Aviral212011/INDIKEY/images/Screenshot 2026-07-25 134537.png

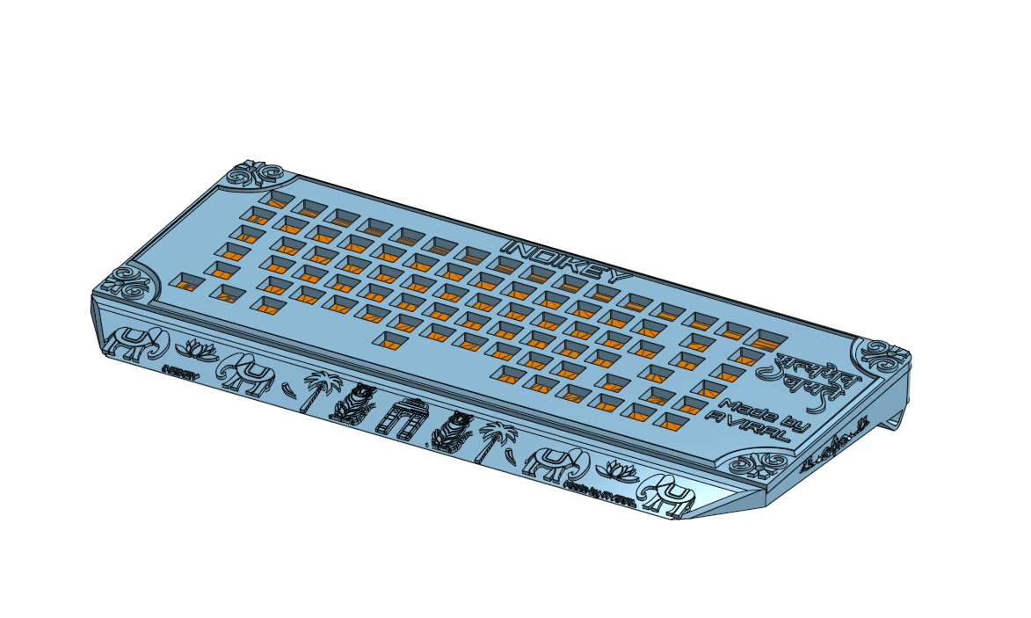
images/Screenshot 2026-07-25 134537.png
