Aviral212011/INDIKEY/images/Screenshot 2026-07-25 135355.png

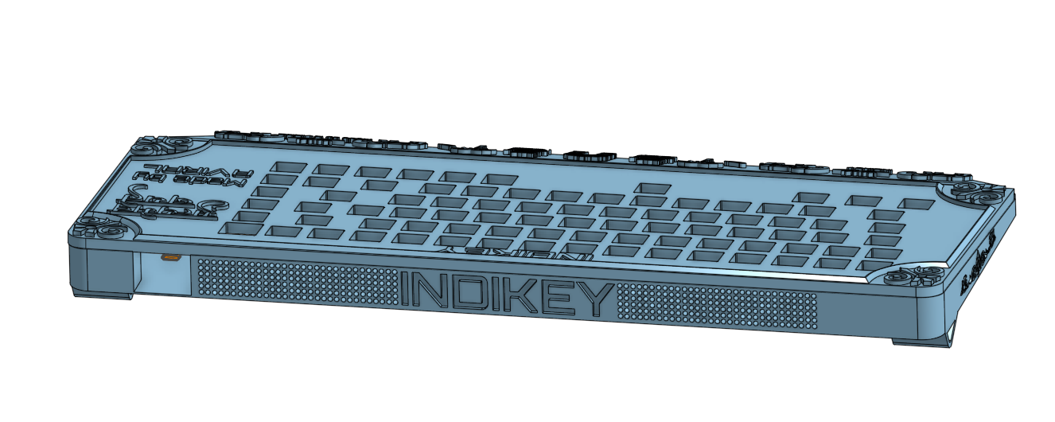
images/Screenshot 2026-07-25 135355.png
