Aviral212011/INDIKEY/images/Screenshot 2026-07-25 135700.png

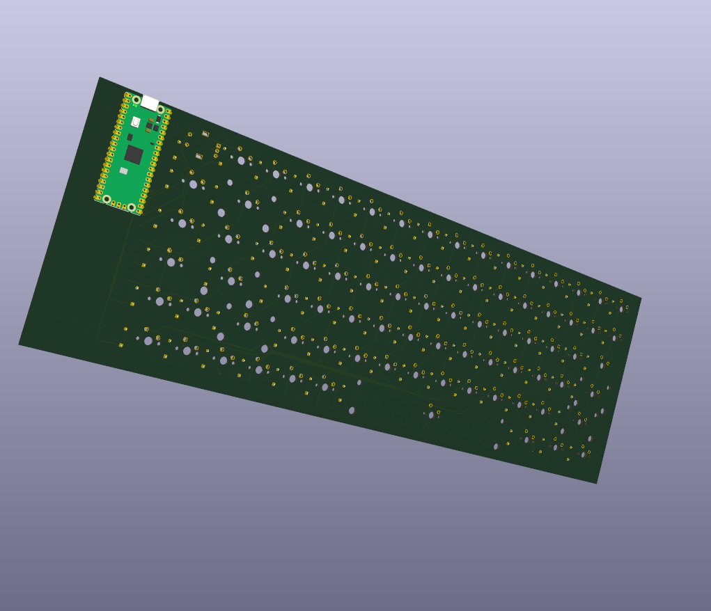
images/Screenshot 2026-07-25 135700.png
