Aviral212011/INDIKEY/images/Screenshot 2026-07-25 135743.png

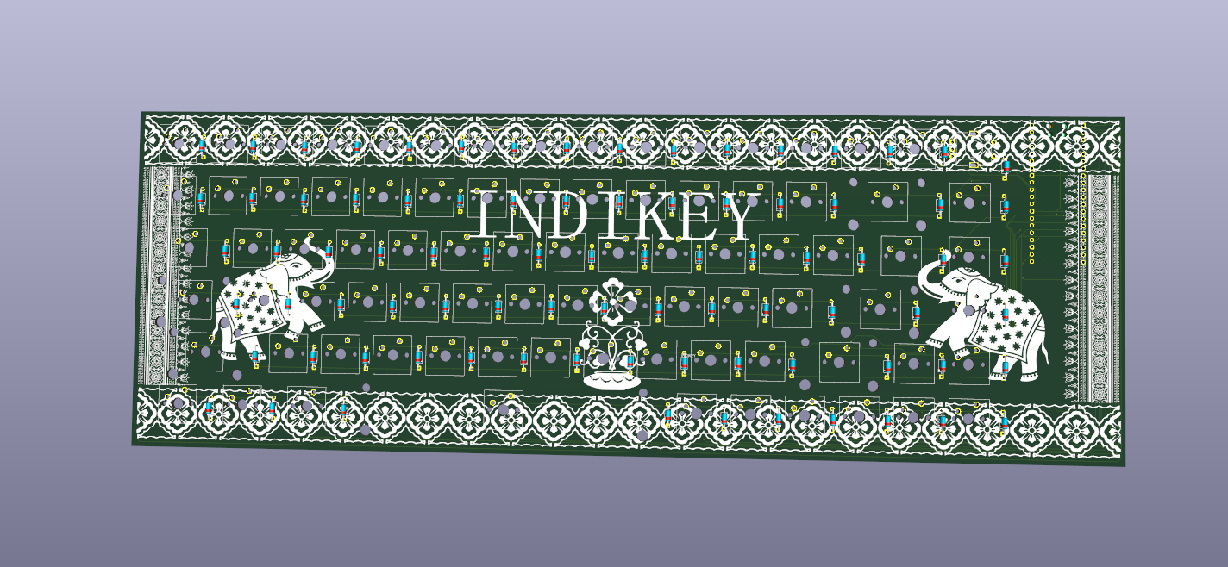
images/Screenshot 2026-07-25 135743.png
