Aviral212011/INDIKEY/images/Screenshot 2026-07-25 140148.png

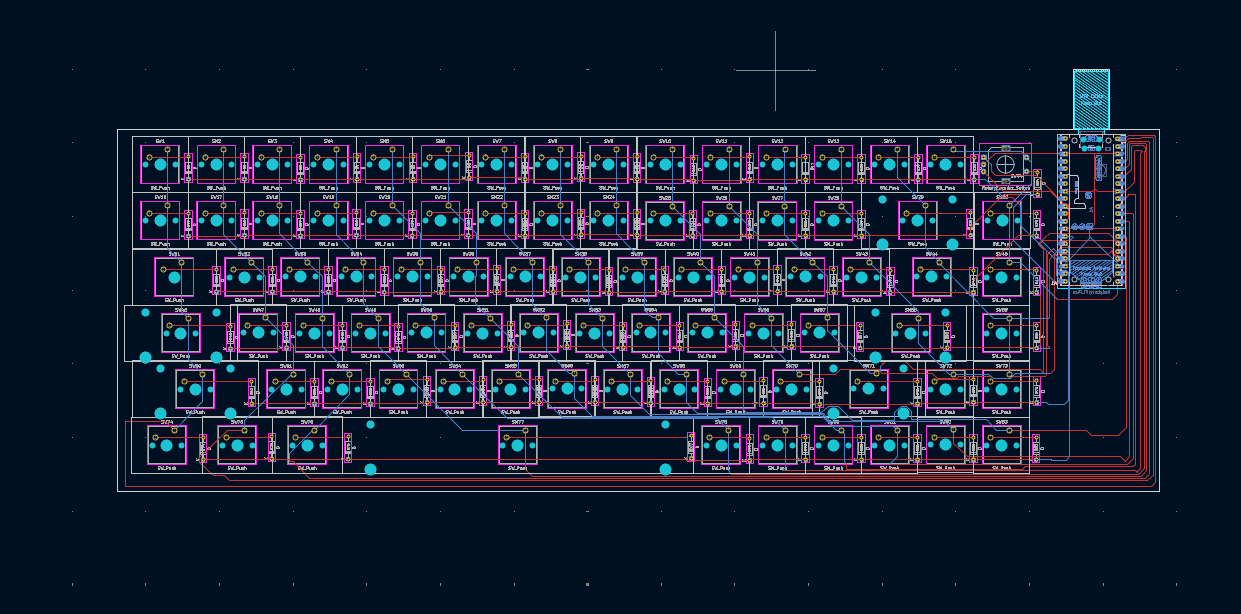
images/Screenshot 2026-07-25 140148.png
